CameraNexus/sitina1/assets/r0p9_bareboard.jpg

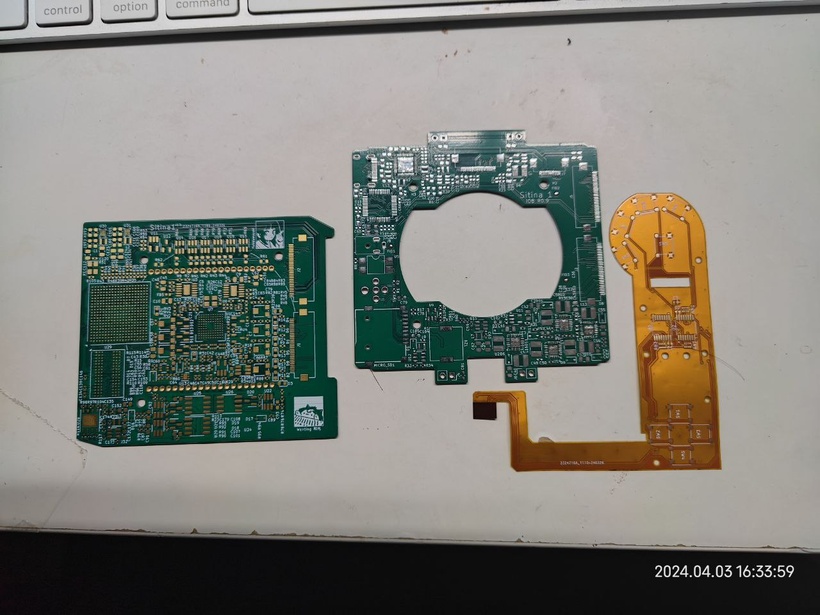
assets/r0p9_bareboard.jpg
