CameraNexus/sitina1/software/postprocessing/LUT/color_cal_blur.png

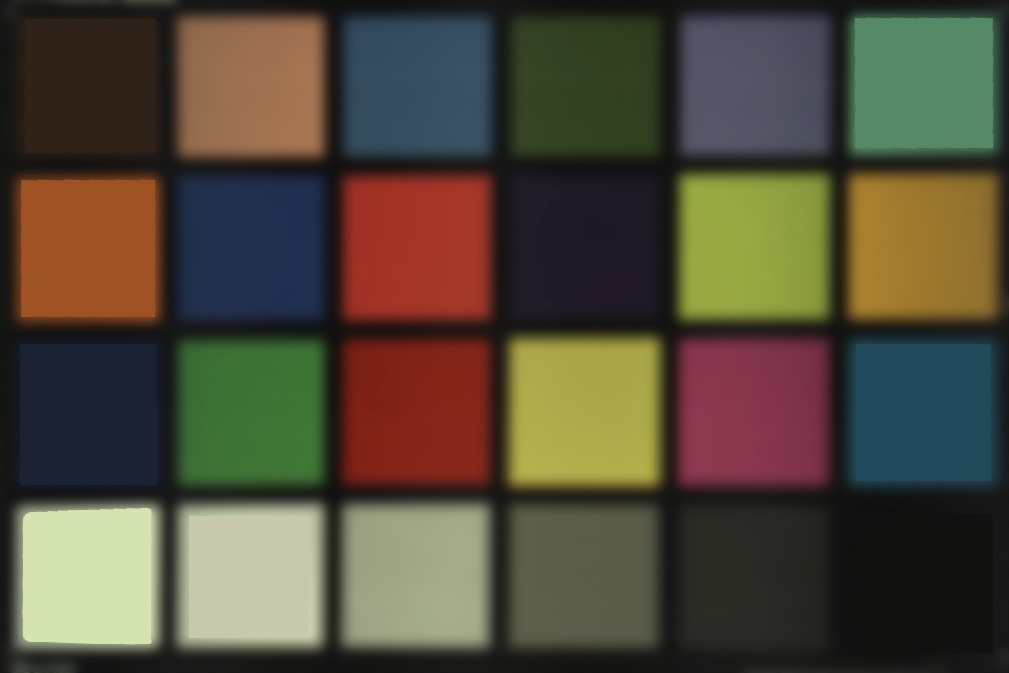
software/postprocessing/LUT/color_cal_blur.png
