CameraNexus/sitina1/software/postprocessing/LUT/cube_lut.png

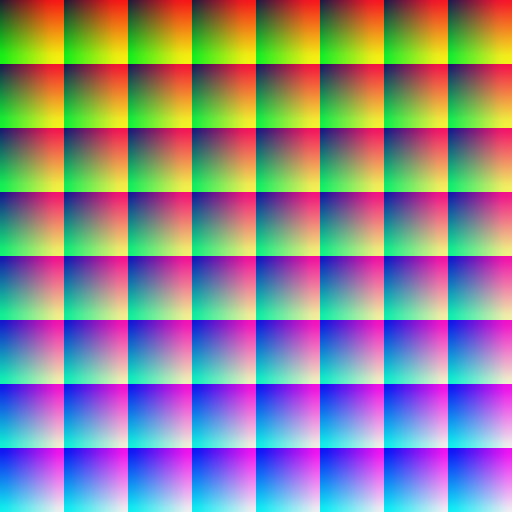
software/postprocessing/LUT/cube_lut.png
