CameraNexus/sitina1/hardware/enclosure/tensionspring.SLDPRT

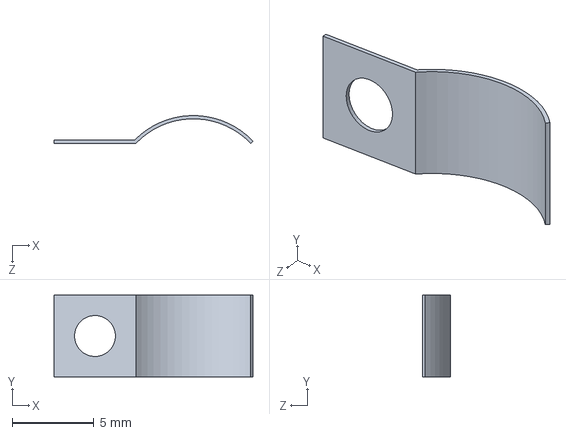
[picture p51: CAD file, 2024-08-05]
hardware/enclosure/tensionspring.SLDPRT
12.1 x 5.00 x 1.70 mm
