CameraNexus/sitina1/hardware/enclosure/gripflex.SLDPRT

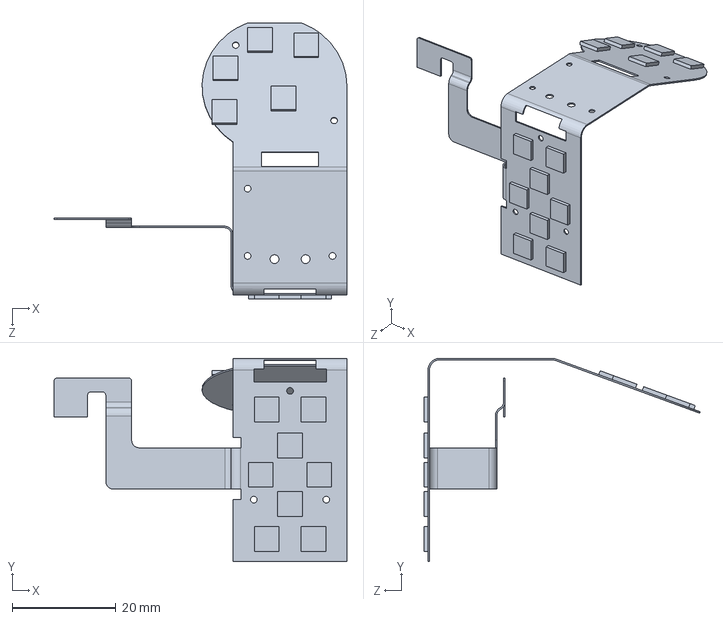
[picture p52: CAD file, 2024-08-05]
hardware/enclosure/gripflex.SLDPRT
56.6 x 39.3 x 53.4 mm
