CameraNexus/sitina1/hardware/enclosure/shutter.SLDPRT

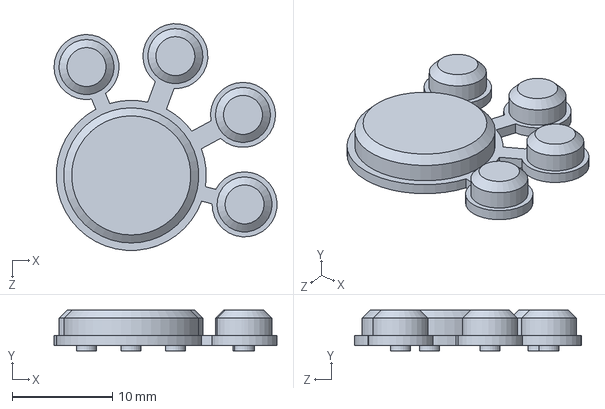
[picture p53: CAD file, 2024-06-10]
hardware/enclosure/shutter.SLDPRT
22.3 x 4.05 x 22.6 mm
