CameraNexus/sitina1/hardware/enclosure/lockpin.SLDPRT

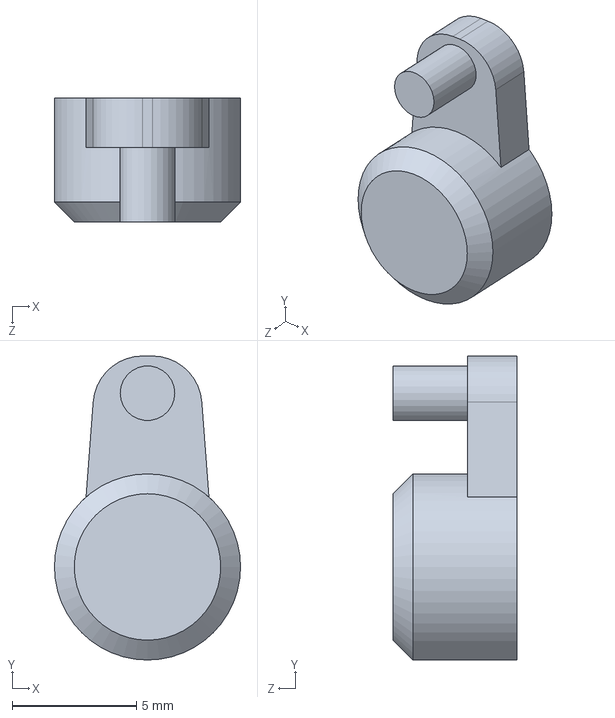
[picture p54: CAD file, 2024-06-10]
hardware/enclosure/lockpin.SLDPRT
7.50 x 12.2 x 5.00 mm
