CameraNexus/sitina1/hardware/enclosure/addbtn.SLDPRT

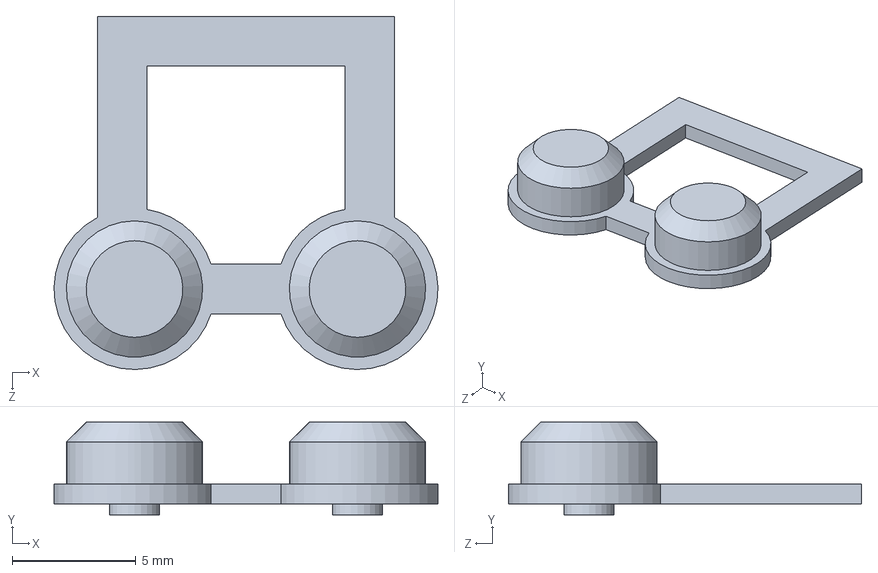
[picture p55: CAD file, 2024-06-10]
hardware/enclosure/addbtn.SLDPRT
15.5 x 3.75 x 14.2 mm
