CameraNexus/sitina1/hardware/enclosure/YZP0652-15072-01.SLDPRT

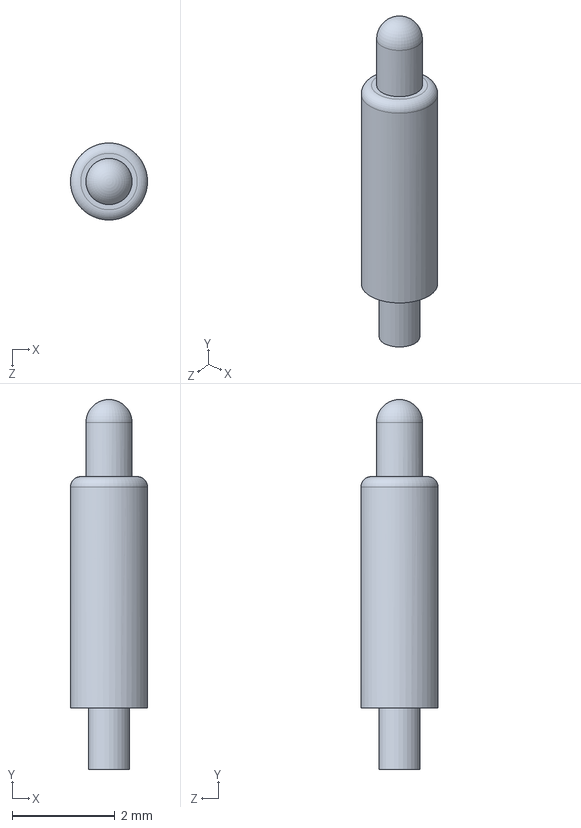
[picture p56: CAD file, 2024-06-10]
hardware/enclosure/YZP0652-15072-01.SLDPRT
1.50 x 7.20 x 1.50 mm
