CameraNexus/sitina1/hardware/enclosure/bayonet.SLDPRT

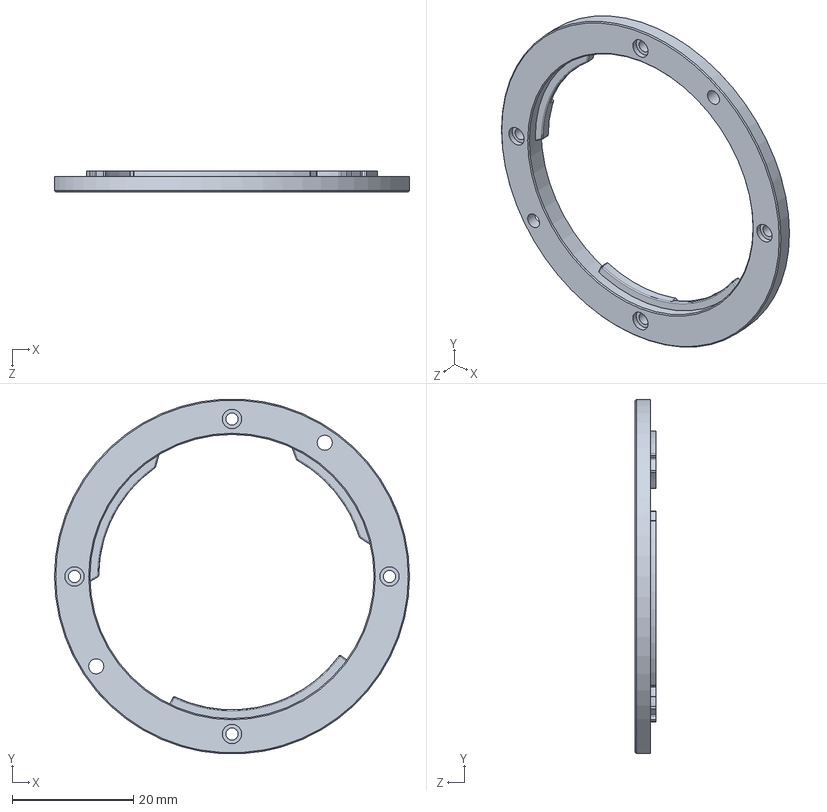
[picture p57: CAD file, 2024-06-10]
hardware/enclosure/bayonet.SLDPRT
58.6 x 58.5 x 3.40 mm
