CameraNexus/sitina1/hardware/enclosure/screencover.SLDPRT

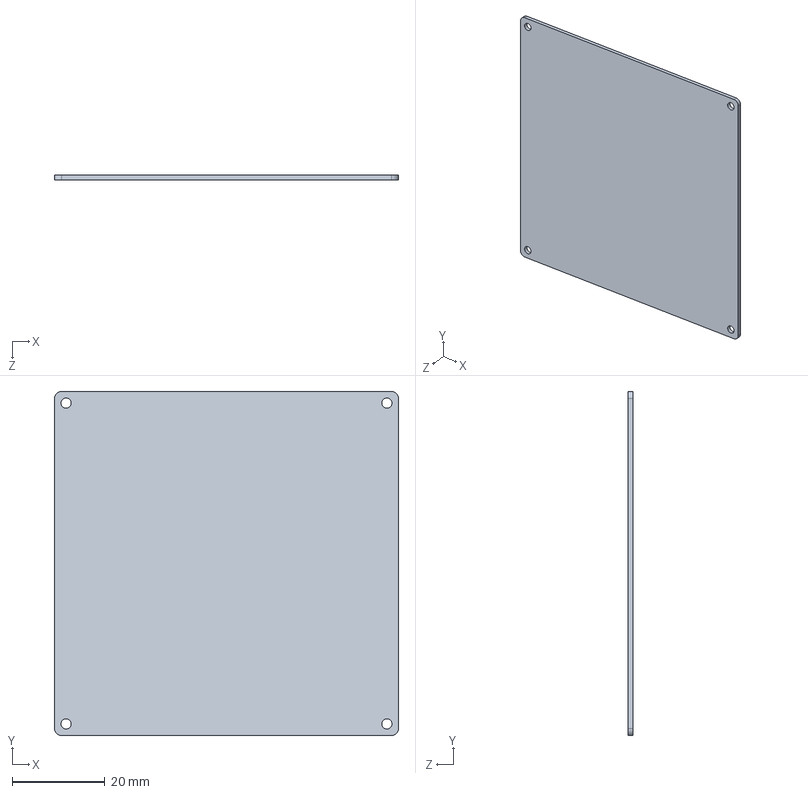
[picture p58: CAD file, 2024-03-25]
hardware/enclosure/screencover.SLDPRT
74.0 x 74.0 x 1.00 mm
