CameraNexus/sitina1/hardware/enclosure/ytc1p-4520.SLDPRT

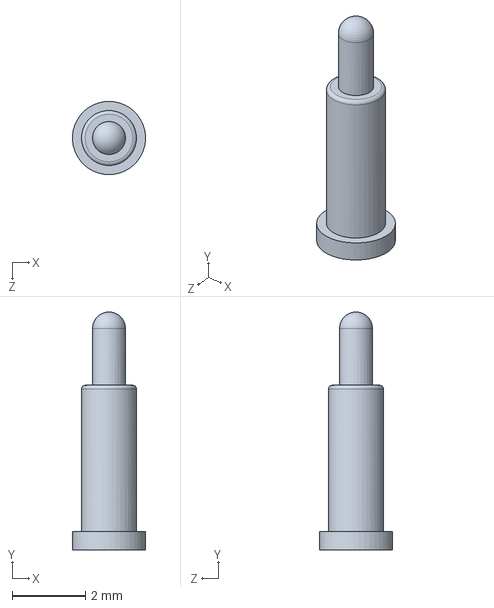
[picture p59: CAD file, 2024-03-02]
hardware/enclosure/ytc1p-4520.SLDPRT
1.99 x 6.50 x 2.00 mm
