CameraNexus/sitina1/hardware/enclosure/shscreen.SLDPRT

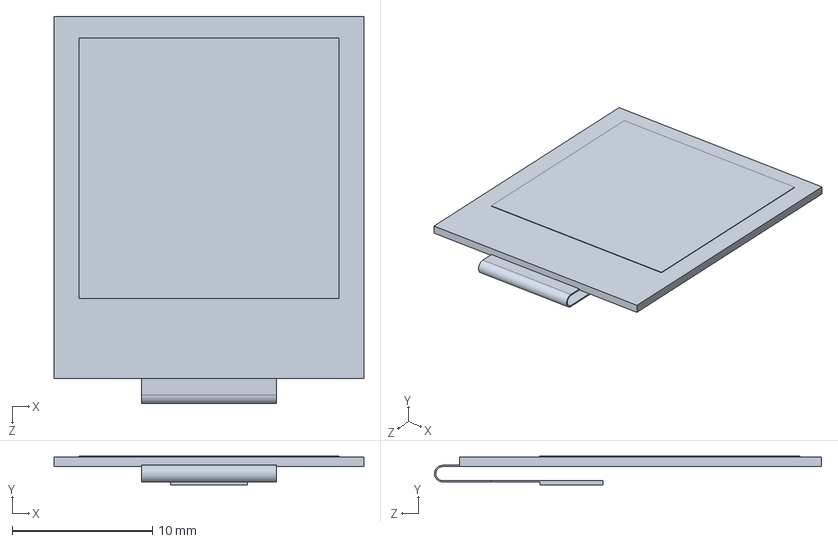
[picture p60: CAD file, 2024-03-02]
hardware/enclosure/shscreen.SLDPRT
22.1 x 2.05 x 27.6 mm
