CameraNexus/sitina1/firmware/ap/.peers.ini

DefaultTarget=true
ServiceManagerID=60d53427-b886-4418-9275-2b21b73e6ee4
TransportName=TCP
AutoSetJtagFrequency=false
PeerTypeId=LINUX_EMULATION
UserName=wenting
Port=1440
Host=127.0.0.1
OSName=Linux
ID=LinuxEmulation
AgentID=60d53427-b886-4418-9275-2b21b73e6ee4
Name=LinuxEmulation

DefaultTarget=true
ServiceManagerID=60d53427-b886-4418-9275-2b21b73e6ee4
TransportName=TCP
AutoSetJtagFrequency=false
PeerTypeId=XRT_SERVER
UserName=wenting
Port=1222
Host=127.0.0.1
OSName=Linux
ID=XRTServer
AgentID=60d53427-b886-4418-9275-2b21b73e6ee4
Name=XRTServer

DefaultTarget=true
ServiceManagerID=60d53427-b886-4418-9275-2b21b73e6ee4
TransportName=TCP
AutoSetJtagFrequency=true
PeerTypeId=HARDWARE_SERVER
UserName=wenting
Port=3121
Host=127.0.0.1
OSName=Linux
ID=Local
AgentID=60d53427-b886-4418-9275-2b21b73e6ee4
Name=Local

DefaultTarget=true
ServiceManagerID=60d53427-b886-4418-9275-2b21b73e6ee4
TransportName=TCP
AutoSetJtagFrequency=false
PeerTypeId=LINUX_TCF_AGENT
UserName=wenting
Port=1534
Host=192.168.0.1
OSName=Linux
ID=Linux Agent
AgentID=60d53427-b886-4418-9275-2b21b73e6ee4
Name=Linux Agent

DefaultTarget=true
ServiceManagerID=60d53427-b886-4418-9275-2b21b73e6ee4
TransportName=TCP
AutoSetJtagFrequency=false
PeerTypeId=QEMU_TCF_GDB_CLIENT
UserName=wenting
Port=1138
Host=127.0.0.1
OSName=Linux
ID=QEMU
AgentID=60d53427-b886-4418-9275-2b21b73e6ee4
Name=QEMU
