CameraNexus/sitina1/gateware/rtl/ccdtimgen.v

`timescale 1ns / 1ps
`default_nettype none
`include "mu_defines.vh"
//
// ccdtimgen.v: CCD Timing Generator
//
// Copyright 2024 Wenting Zhang <zephray@outlook.com>
//
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

module ccdtimgen(
    input  wire         clk,
    input  wire         clk_ccd, // 4X pixel clock
    input  wire         rst,
    input  wire         rst_ccd,
    input  wire         ref_clk, // 1X pixel clock for synchronization
    // APB device port for register access
    /* verilator lint_off UNUSEDSIGNAL */
    `APB_SLAVE_IF,
    /* verilator lint_on UNUSEDSIGNAL */
    // To AFE
    output reg          dvp_hsync,
    output reg          dvp_vsync,
    // To CCD driver
    output reg          tcon_v1,
    output reg          tcon_v2,
    output reg          tcon_v23,
    output reg          tcon_fdg,
    output reg          tcon_strobe,
    output reg          tcon_h1,
    output reg          tcon_h2,
    output reg          tcon_rg
);

    // We run the CCD at 27MHz, or around 37ns pixel time
    // This logic runs at 4x CCD clock (108MHz, 9.26ns) to provide subpixel timing
    // Minimum pulse possible is then 9.26ns, used for RG

    localparam CNTW = 15; // Width of counters

    // Registers
    localparam CCDTG_REG_CTRL           = 16'h0;
    localparam CCDTG_REG_DELAY_HTIME    = 16'h4;
    localparam CCDTG_REG_DELAY_VTIME    = 16'h8;
    localparam CCDTG_REG_ESHUT_LINE     = 16'hC;

    reg tgen_en_apb_clk; // default 0: enable timing gen
    reg tgen_rst_apb_clk; // default 0: reset timing gen
    reg tgen_embed_eshut_apb_clk; // default 1: Embed eshut in field
    reg tgen_start_eshut_apb_clk; // default 0: Use eshut at start of the frame
    reg [CNTW-1:0] delay_htime_apb_clk; // Start delay (for eshut) line length
    reg [CNTW-1:0] delay_vtime_apb_clk; // Start delay (for eshut) line count
    reg [3:0] vskip_apb_clk; // Line skipping factor
    reg [CNTW-1:0] eshut_line_apb_clk; // Line when embed eshut kicks in
    reg tgen_ccd_oen_apb_clk; // default 0: enable CCD timing output
    reg tgen_sync_oen_apb_clk; // default 0: enable HV sync output

    always @(posedge clk) begin
        if (s_apb_penable && s_apb_pwrite && s_apb_psel) begin
            case (s_apb_paddr[15:0])
            CCDTG_REG_CTRL: begin
                tgen_en_apb_clk <= s_apb_pwdata[0];
                tgen_rst_apb_clk <= s_apb_pwdata[1];
                tgen_embed_eshut_apb_clk <= s_apb_pwdata[2];
                tgen_start_eshut_apb_clk <= s_apb_pwdata[3];
                vskip_apb_clk <= s_apb_pwdata[7:4];
                tgen_ccd_oen_apb_clk <= s_apb_pwdata[8];
                tgen_sync_oen_apb_clk <= s_apb_pwdata[9];
            end
            CCDTG_REG_DELAY_HTIME: delay_htime_apb_clk <= s_apb_pwdata[CNTW-1:0];
            CCDTG_REG_DELAY_VTIME: delay_vtime_apb_clk <= s_apb_pwdata[CNTW-1:0];
            CCDTG_REG_ESHUT_LINE: eshut_line_apb_clk <= s_apb_pwdata[CNTW-1:0];
            default: ;
            endcase
        end

        if (rst) begin
            tgen_en_apb_clk <= 1'b0;
            tgen_rst_apb_clk <= 1'b0;
            tgen_embed_eshut_apb_clk <= 1'b1;
            tgen_start_eshut_apb_clk <= 1'b0;
            delay_htime_apb_clk <= 'd10;
            delay_vtime_apb_clk <= 'd10;
            vskip_apb_clk <= 'd6;
            eshut_line_apb_clk <= 'd98;
        end
    end

    assign s_apb_pready = 1'b1;
    assign s_apb_prdata = 32'hdeadbeef; // no readback


    wire tgen_en;
    wire tgen_rst;
    wire tgen_embed_eshut_pre;
    wire tgen_start_eshut_pre;
    wire [CNTW-1:0] delay_htime;
    wire [CNTW-1:0] delay_vtime;
    wire [3:0] vskip_pre;
    wire [CNTW-1:0] eshut_line_pre;
    wire tgen_ccd_oen;
    wire tgen_sync_oen;

    mu_dbsync #(1) tgen_en_sync (clk, clk_ccd, tgen_en_apb_clk, tgen_en);
    mu_dbsync #(1) tgen_rst_sync (clk, clk_ccd, tgen_rst_apb_clk, tgen_rst);
    mu_dbsync #(1) tgen_embed_eshut_sync (clk, clk_ccd, tgen_embed_eshut_apb_clk, tgen_embed_eshut_pre);
    mu_dbsync #(1) tgen_start_eshut_sync (clk, clk_ccd, tgen_start_eshut_apb_clk, tgen_start_eshut_pre);
    mu_dbsync #(CNTW) delay_htime_sync (clk, clk_ccd, delay_htime_apb_clk, delay_htime);
    mu_dbsync #(CNTW) delay_vtime_sync (clk, clk_ccd, delay_vtime_apb_clk, delay_vtime);
    mu_dbsync #(4) vskip_sync (clk, clk_ccd, vskip_apb_clk, vskip_pre);
    mu_dbsync #(CNTW) eshut_line_sync (clk, clk_ccd, eshut_line_apb_clk, eshut_line_pre);
    mu_dbsync #(1) tgen_ccd_oen_sync (clk, clk_ccd, tgen_ccd_oen_apb_clk, tgen_ccd_oen);
    mu_dbsync #(1) tgen_sync_oen_sync (clk, clk_ccd, tgen_sync_oen_apb_clk, tgen_sync_oen);

    // These can be synthesize-time constants
    // See pg. 26 for values, comment labed as min-nom-max
    // See fig. 17 for timing diagram
    wire [CNTW-1:0] t3p = 3240 * 4; // 100-120-200 us
    wire [CNTW-1:0] tv3rd = 270 * 4; // 8-10-15 us
    wire [CNTW-1:0] t3d = 540 * 4 ; // 15-20-80 us
    wire [CNTW-1:0] tl = 2040 * 4;
    wire [CNTW-1:0] tve = 4; // 0-na-100 ns
    wire [CNTW-1:0] tvccd = 94 * 4; // 3-3.5-20 us
    wire [CNTW-1:0] thd = 94 * 4; // 3-3.5-10 us
    wire [CNTW-1:0] th = 4; // TH is always 1 pixel time
    // See fig. 29 for timing diagram
    wire [CNTW-1:0] tfd = 47 * 4; // 0.5-na-na us, typically around half tvccd
    // See fig. 30 for timing diagram
    wire [CNTW-1:0] ts = 108 * 4; // 3-4-10 us
    wire [CNTW-1:0] tsd = 40 * 4; // 1-1.5-10 us
    // Resolution settings
    wire [CNTW-3:0] hpix = 2040 + 24 - 1; // Total horizontal pixel cycles
`ifdef SIM
    wire [CNTW-1:0] vpix = 10 - 1;
`else
    wire [CNTW-1:0] vpix = 2721 - 1;
`endif
    //
    wire [CNTW-1:0] hsw = 256;

    // T3P + TV3RD + TL should be dividable by 4
    // TVCCD + THD should be diviable by 4
    // TL should be dividable by 4
    // TFD should be dividable by 4

    // Track reference 1X clock change
    reg last_ref_clk;
    reg reg_ref_clk;
    always @(posedge clk_ccd) begin
        reg_ref_clk <= ref_clk;
        last_ref_clk <= reg_ref_clk;
    end
    wire ref_in_phase = !last_ref_clk && reg_ref_clk;

    reg [CNTW-1:0] h_cnt;
    reg [CNTW-1:0] v_cnt;
    reg [3:0] v_cnt_sub; // Counter for line skipping

    // Settings need to be updated only during VSYNC
    reg tgen_embed_eshut;
    reg tgen_start_eshut;
    reg [3:0] vskip;
    reg [CNTW-1:0] eshut_line;

    reg hsync;
    reg vsync;

    reg [2:0] state;
    localparam STATE_IDLE = 3'd0;
    localparam STATE_DELAY = 3'd1;
    localparam STATE_1STLINE = 3'd2; // V2 pulse start
    localparam STATE_HFP = 3'd3;
    localparam STATE_ACTIVE = 3'd4;
    localparam STATE_HBP = 3'd5;
    localparam STATE_ESHUT = 3'd6;
    localparam STATE_LINESKIP = 3'd7;

    always @(posedge clk_ccd) begin
        case (state)
        STATE_IDLE: begin
            // Set idle state
            h_cnt <= 'd0;
            v_cnt <= 'd0;

            hsync <= 1'b0;
            vsync <= 1'b0;

            tgen_embed_eshut <= tgen_embed_eshut_pre;
            tgen_start_eshut <= tgen_start_eshut_pre;
            eshut_line <= eshut_line_pre;
            vskip <= vskip_pre;

            if (tgen_en && ref_in_phase) begin
                if (tgen_start_eshut) begin
                    // Apply eshut and wait first
                    state <= STATE_ESHUT;
                end
                else begin
                    // Starts shift out directly
                    state <= STATE_1STLINE;
                end
            end
        end
        STATE_DELAY: begin
            h_cnt <= h_cnt + 'd1;
            if (h_cnt == delay_htime) begin
                h_cnt <= 'd0;
                v_cnt <= v_cnt + 'd1;
                if (v_cnt == delay_vtime) begin
                    v_cnt <= 'd0;
                    state <= STATE_1STLINE;
                end
            end
        end
        STATE_1STLINE: begin
            // This stage only happens during the start of a frame
            // The V2 line is pulsed to transfer pixels from photosensitive
            // region to storage region for readout
            h_cnt <= h_cnt + 'd1;
            if (h_cnt == (t3p + tv3rd + tl - 'd1)) begin
                h_cnt <= 'd0;
                state <= STATE_HFP;
                vsync <= 1'b1;
            end
        end
        STATE_HFP: begin
            h_cnt <= h_cnt + 'd1;
            hsync <= (h_cnt < hsw);
            if (h_cnt == (tvccd + thd - 'd1)) begin
                h_cnt <= 'd0;
                state <= STATE_ACTIVE;
            end
        end
        STATE_ACTIVE: begin
            // Stage for pixel shift out
            h_cnt <= h_cnt + 'd1;
            if (h_cnt == {hpix, 2'b11}) begin
                h_cnt <= 'd0;
                state <= STATE_HBP;
            end
        end
        STATE_HBP: begin
            h_cnt <= h_cnt + 'd1;
            if (h_cnt == (th - 'd1)) begin
                h_cnt <= 'd0;
                v_cnt <= v_cnt + 'd1;
                if (v_cnt < vpix) begin
                    if (vskip != 'd0)
                        state <= STATE_LINESKIP;
                    else if (tgen_embed_eshut && (v_cnt == eshut_line))
                        state <= STATE_ESHUT;
                    else
                        state <= STATE_HFP;
                    vsync <= 1'b0;
                end
                else begin
                    // Update settings on VSYNC
                    tgen_embed_eshut <= tgen_embed_eshut_pre;
                    tgen_start_eshut <= tgen_start_eshut_pre;
                    eshut_line <= eshut_line_pre;
                    vskip <= vskip_pre;
                    v_cnt <= 'd0;
                    if (tgen_en) begin
                        if (tgen_start_eshut_pre) begin
                            // Apply eshut and wait first
                            state <= STATE_ESHUT;
                        end
                        else begin
                            // Starts shift out directly
                            state <= STATE_1STLINE;
                        end
                    end
                end
            end
        end
        STATE_ESHUT: begin
            h_cnt <= h_cnt + 'd1;
            if (h_cnt == (ts + tsd - 'd1)) begin
                h_cnt <= 'd0;
                if (tgen_start_eshut)
                    // This eshut is applied at the start of the frame
                    state <= STATE_DELAY;
                else
                    state <= STATE_HFP;
            end
        end
        STATE_LINESKIP: begin
            // Line skipping is a bit involved... it needs to wait additional TFD time
            h_cnt <= h_cnt + 'd1;
            if (v_cnt_sub == 'd0) begin
                // First line is just TFD
                if (h_cnt == (tfd - 'd1)) begin
                    h_cnt <= 'd0;
                    v_cnt_sub <= v_cnt_sub + 'd1;
                end
            end
            else begin
                // Normal counting
                if (h_cnt == (tvccd + thd - 'd1)) begin
                    h_cnt <= 'd0;
                    v_cnt_sub <= v_cnt_sub + 'd1;
                    if (v_cnt_sub == vskip) begin
                        v_cnt_sub <= 'd0;
                        state <= STATE_HFP;
                    end
                    v_cnt <= v_cnt + 'd1;
                end
            end
        end
        endcase

        if (rst_ccd) begin
            state <= STATE_IDLE;
            h_cnt <= 'd0;
            v_cnt <= 'd0;
            hsync <= 1'b0;
            vsync <= 1'b0;
        end
    end

    reg v1, v2, v23, fdg, strobe, h1, h2, rg;
    always @(*) begin
        // Set default inactive value
        v1 = 1'b1;
        v2 = 1'b0;
        v23 = 1'b0;
        fdg = 1'b0;
        h1 = 1'b1;
        h2 = 1'b0;
        rg = 1'b0;
        strobe = 1'b0;

        case (state)
        STATE_DELAY: begin
            rg = (h_cnt[1:0] == 2'b00);
        end
        STATE_1STLINE: begin
            v1 = !((h_cnt >= t3p) && (h_cnt < (t3p + tv3rd - tve)));
            v2 = (h_cnt < (t3p + tv3rd + t3d));
            v23 = ((h_cnt >= (t3p - tve)) && (h_cnt < (t3p + tv3rd)));
            rg = (h_cnt[1:0] == 2'b00);
        end
        STATE_HFP: begin
            v1 = !((h_cnt >= tve) && (h_cnt < (tvccd - tve)));
            v2 = h_cnt < tvccd;
            rg = (h_cnt[1:0] == 2'b00);
        end
        STATE_ACTIVE: begin
            h1 = (h_cnt[1] == 1'b0);
            h2 = (h_cnt[1] == 1'b1);
            rg = (h_cnt[1:0] == 2'b00);
        end
        STATE_HBP: begin
            rg = (h_cnt[1:0] == 2'b00);
        end
        STATE_ESHUT: begin
            strobe = (h_cnt < ts);
            rg = (h_cnt[1:0] == 2'b00);
        end
        STATE_LINESKIP: begin
            if (v_cnt_sub == 'd0) begin
                fdg = 1'b1;
            end
            else begin
                v1 = !((h_cnt >= tve) && (h_cnt < (tvccd - tve)));
                v2 = h_cnt < tvccd;
                if (v_cnt_sub == vskip) begin
                    // Last line to skip
                    fdg = (h_cnt < (tvccd + thd - tfd));
                end
                else begin
                    fdg = 1'b1;
                end
            end
            rg = (h_cnt[1:0] == 2'b00);
        end
        default: ;
        endcase
    end

    always @(posedge clk_ccd) begin
        if (rst_ccd || !tgen_ccd_oen) begin
            tcon_v1 <= 1'b0;
            tcon_v2 <= 1'b1;
            tcon_v23 <= 1'b1;
            tcon_fdg <= 1'b1;
            tcon_h1 <= 1'b1;
            tcon_h2 <= 1'b0;
            tcon_rg <= 1'b0;
            tcon_strobe <= 1'b1;
        end
        else begin
            tcon_v1 <= !v1;
            tcon_v2 <= !v2;
            tcon_v23 <= !v23;
            tcon_fdg <= fdg;
            tcon_h1 <= h1;
            tcon_h2 <= h2;
            tcon_rg <= rg;
            tcon_strobe <= !strobe;
        end

        if (rst_ccd || !tgen_sync_oen) begin
            dvp_hsync <= 1'b1;
            dvp_vsync <= 1'b1;
        end
        else begin
            dvp_hsync <= !hsync;
            dvp_vsync <= !vsync;
        end
    end

    wire tgen_running = state != STATE_IDLE;

endmodule

`default_nettype wire
