CameraNexus/sitina1/gateware/rtl/system.v

`timescale 1ns / 1ps
`default_nettype none
`include "mu_defines.vh"
//
// system.v: Portable system top level
//
// Copyright 2024 Wenting Zhang <zephray@outlook.com>
//
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
module system #(
    parameter AXI_AW = 32,
    parameter AXI_DW = 64,
    parameter AXI_IDW = 1
) (
    input  wire         clk,        // Clock
    input  wire         clk_ccd_4x, // CCD 4X pixel clock
    input  wire         clk_ccd_1x, // CCD 1X pixel clock
    input  wire         clk_lcd,    // LCD pixel clock
    input  wire         rst,
    input  wire         rst_ccd,
    input  wire         rst_lcd,
    // DVP from AD9990
    input  wire [13:0]  dvp_d,
    output wire         dvp_hsync,
    output wire         dvp_vsync,
    input  wire         dvp_pclk,
    input  wire         dvp_rst,
    // AD9990 control
    output wire         afe_rst,
    output wire         afe_sync,
    output wire         afe_sdata,
    output wire         afe_sl,
    output wire         afe_sck,
    // MIPI DSI for LCD
    output wire         dsi_lp_cp,
    output wire         dsi_lp_cn,
    output wire [1:0]   dsi_lp_dp,
    output wire [1:0]   dsi_lp_dn,
    output wire [15:0]  dsi_hs_dat,
    output wire         dsi_hsck_ten,
    output wire         dsi_hsdat_ten,
    // TCON for CCD
    output wire         tcon_v1,
    output wire         tcon_v2,
    output wire         tcon_v23,
    output wire         tcon_fdg,
    output wire         tcon_strobe,
    output wire         tcon_h1,
    output wire         tcon_h2,
    output wire         tcon_rg,
    // Power control
    output wire         vab_pwm,
    // I2C
    output wire         i2c_pl0_scl_oe,
    output wire         i2c_pl0_scl_o,
    input  wire         i2c_pl0_scl_i,
    output wire         i2c_pl0_sda_oe,
    output wire         i2c_pl0_sda_o,
    input  wire         i2c_pl0_sda_i,
    output wire         i2c_pl1_scl_oe,
    output wire         i2c_pl1_scl_o,
    input  wire         i2c_pl1_scl_i,
    output wire         i2c_pl1_sda_oe,
    output wire         i2c_pl1_sda_o,
    input  wire         i2c_pl1_sda_i,
    // APB device port for register access
    `APB_SLAVE_IF,
    // AXI host port for memory access
    `AXI_MASTER_IF(AXI_AW, AXI_DW, AXI_IDW)
);

    // Number of APB devices
    localparam APB_N = 5;

    // Internal APB for register access
    wire regbus_pwrite;
    wire [31:0] regbus_pwdata;
    wire [31:0] regbus_paddr;
    wire regbus_penable;
    wire [APB_N-1:0] regbus_psel_vec;
    wire [APB_N-1:0] regbus_pready_vec;
    wire [APB_N*32-1:0] regbus_prdata_vec;

	apbbus #(
        .N(APB_N)
    ) apbbus (
        // Interface to APB master
        .up_pwrite(s_apb_pwrite),
        .up_pwdata(s_apb_pwdata),
        .up_paddr(s_apb_paddr),
        .up_penable(s_apb_penable),
        .up_psel(s_apb_psel),
        .up_pready(s_apb_pready),
        .up_prdata(s_apb_prdata),
        // Interface to APB slaves
        .down_pwrite(regbus_pwrite),
        .down_pwdata(regbus_pwdata),
        .down_paddr(regbus_paddr),
        .down_penable(regbus_penable),
        .down_psel_vec(regbus_psel_vec),
        .down_pready_vec(regbus_pready_vec),
        .down_prdata_vec(regbus_prdata_vec)
    );

    /* verilator lint_off UNUSEDSIGNAL */
    wire [31:0] gpio_out;
    wire [31:0] gpio_in;
    wire [31:0] gpio_oe;
    /* verilator lint_on UNUSEDSIGNAL */
    mu_gpio mu_gpio (
        .clk(clk),
        .rst(rst),
        // APB device port for register access
        `APB_SLAVE_CONN(regbus_, 0),
        // GPIO
        .gpio_out(gpio_out),
        .gpio_in(gpio_in),
        .gpio_oe(gpio_oe)
    );

    assign afe_rst = gpio_out[0];
    assign afe_sync = gpio_out[1];
    assign afe_sdata = gpio_out[2];
    assign afe_sl = gpio_out[3];
    assign afe_sck = gpio_out[4];

    wire dsi_lp_sel = gpio_out[5];
    wire dsi_lp_gpio_cp = gpio_out[6];
    wire dsi_lp_gpio_cn = gpio_out[7];
    wire [1:0] dsi_lp_gpio_dp = gpio_out[9:8];
    wire [1:0] dsi_lp_gpio_dn = gpio_out[11:10];

    assign i2c_pl0_scl_o = gpio_out[12];
    assign i2c_pl0_sda_o = gpio_out[13];
    assign i2c_pl0_scl_oe = gpio_oe[12];
    assign i2c_pl0_sda_oe = gpio_oe[13];
    assign gpio_in[12] = i2c_pl0_scl_i;
    assign gpio_in[13] = i2c_pl0_sda_i;
    assign i2c_pl1_scl_o = gpio_out[14];
    assign i2c_pl1_sda_o = gpio_out[15];
    assign i2c_pl1_scl_oe = gpio_oe[14];
    assign i2c_pl1_sda_oe = gpio_oe[15];
    assign gpio_in[14] = i2c_pl1_scl_i;
    assign gpio_in[15] = i2c_pl1_sda_i;

    assign gpio_in[11:0] = 'd0;
    assign gpio_in[31:16] = 'd0;

    ccdtimgen ccdtimgen (
        .clk(clk),
        .clk_ccd(clk_ccd_4x),
        .ref_clk(clk_ccd_1x),
        .rst(rst),
        .rst_ccd(rst_ccd),
        // APB device port for register access
        `APB_SLAVE_CONN(regbus_, 1),
        // To AFE
        .dvp_hsync(dvp_hsync),
        .dvp_vsync(dvp_vsync),
        // To CCD driver
        .tcon_v1(tcon_v1),
        .tcon_v2(tcon_v2),
        .tcon_v23(tcon_v23),
        .tcon_fdg(tcon_fdg),
        .tcon_strobe(tcon_strobe),
        .tcon_h1(tcon_h1),
        .tcon_h2(tcon_h2),
        .tcon_rg(tcon_rg)
    );

//    assign tcon_v1 = 1'b0;
//    assign tcon_v2 = 1'b0;
//    assign tcon_v23 = 1'b0;
//    assign tcon_fdg = 1'b0;
//    assign tcon_strobe = 1'b0;
//    assign tcon_h1 = 1'b0;
//    assign tcon_h2 = 1'b0;
//    assign tcon_rg = 1'b0;

    `AXI_WIRES(lcd_, AXI_AW, AXI_DW, AXI_IDW);

    wire dsi_lp_ctl_cp;
    wire dsi_lp_ctl_cn;
    wire [1:0] dsi_lp_ctl_dp;
    wire [1:0] dsi_lp_ctl_dn;
    mu_dsilite #(
        .AXI_AW(AXI_AW),
        .AXI_DW(AXI_DW)
    ) mu_dsilite (
        .clk(clk),
        .clk_pix(clk_lcd),
        .rst(rst),
        .rst_pix(rst_lcd),
        // APB device port for register access
        `APB_SLAVE_CONN(regbus_, 2),
	    // AXI host port for direct memory access
        `AXI_CONN(m_, lcd_),
	    // Display interface
        .dpi_ext_vsync(1'b0),
        // DSI LP, to IO mux
        .dsi_lp_cp(dsi_lp_ctl_cp),
        .dsi_lp_cn(dsi_lp_ctl_cn),
        .dsi_lp_dp(dsi_lp_ctl_dp),
        .dsi_lp_dn(dsi_lp_ctl_dn),
        // DSI HS, to HS serializer / PHY
        .dsi_hs_dat(dsi_hs_dat),
        .dsi_hsck_ten(dsi_hsck_ten),
        .dsi_hsdat_ten(dsi_hsdat_ten)
    );

    // Mux between GPIO LP and controller LP signal
    assign dsi_lp_cp = dsi_lp_sel ? dsi_lp_gpio_cp : dsi_lp_ctl_cp;
    assign dsi_lp_cn = dsi_lp_sel ? dsi_lp_gpio_cn : dsi_lp_ctl_cn;
    assign dsi_lp_dp = dsi_lp_sel ? dsi_lp_gpio_dp : dsi_lp_ctl_dp;
    assign dsi_lp_dn = dsi_lp_sel ? dsi_lp_gpio_dn : dsi_lp_ctl_dn;

    mu_pwmlite #(
        .NCH(1),
        .PSCW(8),
        .CNTW(8)
    ) mu_pwmlite (
        .clk(clk),
        .rst(rst),
        `APB_SLAVE_CONN(regbus_, 3),
        .pwm_out(vab_pwm)
    );

    `AXI_WIRES(cam_, AXI_AW, AXI_DW, AXI_IDW);

    mu_dcif #(
        .AXI_AW(AXI_AW),
        .AXI_DW(AXI_DW)
    ) mu_dcif (
        .clk(clk),
        .rst(rst),
        `APB_SLAVE_CONN(regbus_, 4),
        `AXI_CONN(m_, cam_),
        .dvp_d({dvp_d, 2'b0}),
        .dvp_hsync(dvp_hsync),
        .dvp_vsync(dvp_vsync),
        .dvp_pclk(dvp_pclk),
        .dvp_rst(dvp_rst)
    );

    mu_aximerge #(
        .AXI_AW(AXI_AW),
        .AXI_DW(AXI_DW),
        .AXI_IDW(AXI_IDW)
    ) mu_aximerge (
        .clk(clk),
        .rst(rst),
        `AXI_CONN(srd_, lcd_),
        `AXI_CONN(swr_, cam_),
        `AXI_CONN(m_, m_)
    );

endmodule

`default_nettype wire
