CameraNexus/sitina1/firmware/ap/application/src/hw/mcusvc.c

//
// Sitina 1
// Copyright 2024 Wenting Zhang
//
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
// File : mcusvc.c
// Brief: Service provided by MCU
//
#include <stdint.h>
#include <stdbool.h>
#include "i2c.h"
#include "mcusvc.h"

#define CMD_NOP             0x00
#define CMD_SET_LCD_PWR     0x01
#define CMD_SET_LCD_BL      0x02
#define CMD_FRAMEBUF_XFER   0x03
#define CMD_SET_LED         0x04
#define CMD_POWER_OFF       0x05
#define CMD_GET_BUTTONS     0x80
#define CMD_GET_BAT         0x82    // {voltage[15:0], capacity[15:0]}
#define CMD_GET_PWR         0x83    // {7'd0, is_charging, 8'd0, power[15:0]}

typedef struct {
    uint8_t cmd;
    uint8_t param1;
    uint8_t param2;
    uint8_t param3;
    uint8_t param4;
} DATA_PKT;

#define PKT_SIZE            sizeof(DATA_PKT)
#define FB_SIZE             (128*128/8) // 2KB

#define MCU_I2C             &i2c0
#define MCU_I2C_ADDR        0x20

static uint8_t rotenc_val;

void mcusvc_init(void) {
    // nothing
}

void mcusvc_set_lcd_power(bool en) {
    DATA_PKT pkt = {
        .cmd = CMD_SET_LCD_PWR,
        .param1 = en ? 1 : 0
    };
    i2c_write_payload(MCU_I2C, MCU_I2C_ADDR, (uint8_t *)&pkt, PKT_SIZE);
}

void mcusvc_set_lcd_bl(uint8_t brightness) {
    DATA_PKT pkt = {
        .cmd = CMD_SET_LCD_BL,
        .param1 = brightness
    };
    i2c_write_payload(MCU_I2C, MCU_I2C_ADDR, (uint8_t *)&pkt, PKT_SIZE);
}

void mcusvc_set_led(bool on) {
    DATA_PKT pkt = {
        .cmd = CMD_SET_LED,
        .param1 = on
    };
    i2c_write_payload(MCU_I2C, MCU_I2C_ADDR, (uint8_t *)&pkt, PKT_SIZE);
}

void mcusvc_xfer_fb(uint8_t *fb) {
    // Always do full transfer for now
    DATA_PKT pkt = {
        .cmd = CMD_FRAMEBUF_XFER,
        .param1 = 0,
        .param2 = 0,
        .param3 = 0,
        .param4 = 0
    };
    i2c_write_payload(MCU_I2C, MCU_I2C_ADDR, (uint8_t *)&pkt, PKT_SIZE);
    i2c_write_payload(MCU_I2C, MCU_I2C_ADDR, fb, FB_SIZE);
}

uint32_t mcusvc_get_bat_charge(void) {
    DATA_PKT pkt = {
        .cmd = CMD_GET_BAT,
    };
    int result = i2c_read_payload(MCU_I2C, MCU_I2C_ADDR, (uint8_t *)&pkt,
        PKT_SIZE, (uint8_t *)&pkt, PKT_SIZE);
    if (result < 0)
        return 0;
    return pkt.param1 | ((uint32_t)(pkt.param2) << 8);
}

uint32_t mcusvc_get_bat_voltage(void) {
    DATA_PKT pkt = {
        .cmd = CMD_GET_BAT,
    };
    int result = i2c_read_payload(MCU_I2C, MCU_I2C_ADDR, (uint8_t *)&pkt,
        PKT_SIZE, (uint8_t *)&pkt, PKT_SIZE);
    if (result < 0)
        return 0;
    return pkt.param3 | ((uint32_t)(pkt.param4) << 8);
}

bool mcusvc_get_is_bat_charging(void) {
    DATA_PKT pkt = {
        .cmd = CMD_GET_BAT,
    };
    int result = i2c_read_payload(MCU_I2C, MCU_I2C_ADDR, (uint8_t *)&pkt,
        PKT_SIZE, (uint8_t *)&pkt, PKT_SIZE);
    if (result < 0)
        return false;
    return !!(pkt.param4);
}

uint32_t mcusvc_get_buttons(void) {
    DATA_PKT pkt = {
        .cmd = CMD_GET_BUTTONS,
    };
    int result = i2c_read_payload(MCU_I2C, MCU_I2C_ADDR, (uint8_t *)&pkt,
        PKT_SIZE, (uint8_t *)&pkt, PKT_SIZE);
    if (result < 0)
        return 0x0;
    rotenc_val = *(int8_t *)(&(pkt.param4));
    return pkt.param1 | ((uint32_t)(pkt.param2) << 8) |
        ((uint32_t)(pkt.param3) << 16);
}

int8_t mcusvc_get_rotenc(void) {
    return rotenc_val;
}

void mcusvc_power_off(void) {
    DATA_PKT pkt = {
        .cmd = CMD_POWER_OFF
    };
    i2c_write_payload(MCU_I2C, MCU_I2C_ADDR, (uint8_t *)&pkt, PKT_SIZE);
}
