CameraNexus/sitina1/Firmware/source/MIMXRT1052_Project.c

/*
 * Copyright 2016-2021 NXP
 * All rights reserved.
 *
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
 * o Neither the name of NXP Semiconductor, Inc. nor the names of its
 *   contributors may be used to endorse or promote products derived from this
 *   software without specific prior written permission.
 *
 * THIS SOFTWARE IS PROVIDED BY THE COPYRIGHT HOLDERS AND CONTRIBUTORS "AS IS" AND
 * ANY EXPRESS OR IMPLIED WARRANTIES, INCLUDING, BUT NOT LIMITED TO, THE IMPLIED
 * WARRANTIES OF MERCHANTABILITY AND FITNESS FOR A PARTICULAR PURPOSE ARE
 * DISCLAIMED. IN NO EVENT SHALL THE COPYRIGHT HOLDER OR CONTRIBUTORS BE LIABLE FOR
 * ANY DIRECT, INDIRECT, INCIDENTAL, SPECIAL, EXEMPLARY, OR CONSEQUENTIAL DAMAGES
 * (INCLUDING, BUT NOT LIMITED TO, PROCUREMENT OF SUBSTITUTE GOODS OR SERVICES;
 * LOSS OF USE, DATA, OR PROFITS; OR BUSINESS INTERRUPTION) HOWEVER CAUSED AND ON
 * ANY THEORY OF LIABILITY, WHETHER IN CONTRACT, STRICT LIABILITY, OR TORT
 * (INCLUDING NEGLIGENCE OR OTHERWISE) ARISING IN ANY WAY OUT OF THE USE OF THIS
 * SOFTWARE, EVEN IF ADVISED OF THE POSSIBILITY OF SUCH DAMAGE.
 */

/**
 * @file    MIMXRT1052_Project.c
 * @brief   Application entry point.
 */
#include <stdio.h>
#include "board.h"
#include "peripherals.h"
#include "pin_mux.h"
#include "clock_config.h"
#include "MIMXRT1052.h"
/* TODO: insert other include files here. */

/* TODO: insert other definitions and declarations here. */

/*
 * @brief   Application entry point.
 */
int main(void) {

    /* Init board hardware. */
    BOARD_ConfigMPU();
    BOARD_InitBootPins();
    BOARD_InitBootClocks();
    BOARD_InitBootPeripherals();

    printf("Hello World\n");

    /* Force the counter to be placed into memory. */
    volatile static int i = 0 ;
    /* Enter an infinite loop, just incrementing a counter. */
    while(1) {
        i++ ;
        /* 'Dummy' NOP to allow source level single stepping of
            tight while() loop */
        __asm volatile ("nop");
    }
    return 0 ;
}
